vicharak-in/shrike/docs/reading_list.md

(reading_list)=
# Reading List

This is a compilation of the resources and references suggested for Shrike and FPGA in General across the web. 
 
## 1. Learning Resources 
 
1. [NandLand](https://nandland.com/learn-verilog/)
2. [Learn FPGA - B Levy](https://github.com/BrunoLevy/learn-fpga)
3. [Fpga4Fun](https://www.fpga4fun.com/)
4. [SutherLand Papers](https://sutherland-hdl.com/papers.html)
5. [FPGACPU](http://fpgacpu.ca/)
6. [ZipCpu](https://zipcpu.com/)
7. [Project F](https://projectf.io/)
8. [Verilog Pro](https://www.verilogpro.com/)
9. [AISC WORLD Verilog Tutorials ](https://www.asic-world.com/verilog/veritut.html)
10. [Lawrie FPGA Tutorials](https://lawrie.github.io/blackicemxbook/)
11. [Lut4](https://lut4.com/) 

## 2. Similar Hardware Projects 
1. [Ulx3s-Project](https://ulx3s.github.io/)
2. [TinyFPGA-Project](https://tinyfpga.com/)
3. [icebreaker-Project](https://github.com/icebreaker-fpga/icebreaker)
4. [pico-ice](https://pico-ice.tinyvision.ai/)

## 3. Communities to Join
1. Vicharak
2. ULX3S
3. TinyVision
4. 1bitsquared
