vicharak-in/shrike/Docs/index.rst

.. _shrike-home:

..
   Vicharak master file, created by
   sphinx-quickstart on Tue May  9 19:32:34 2023.
   You can adapt this file completely to your liking, but it should at least
   contain the root `toctree` directive.

.. rst-class:: lead

##############################################
 Welcome to Shrike-lite  FPGA's documentation!
##############################################

Shrike-lite is lighter version of world's first fully open source FPGA Dev board crowdsupply releasing on CrowdSupply Renesas Forge FPGA SLG47910 and RP2350.

We at vicharak have kept in mind need of a learner, maker and a hobbyist while designing this art. This dev board will be your stepping stone in the field of FPGA , reconfigurable and heterogenous computing.



.. toctree::
   :glob:
   :caption: Contents
   :titlesonly:

   Introduction <introduction>
   Hardware Overview <hardware_overview>
   Getting Started <getting_started> 
   Tools Setup <tools_setup_guide>
   Generating Bitstream <generating_your_first_bitstream>
   Verilog Style Guide <verilog_style_guide>      
   Shrike Pinouts <shrike_pinouts>
   Shrike CLI Guide <shrike_cli_guide>
   Reading List <reading_list>

.. note::

   We welcome contributions and bug reports through our `GitHub
   repository <https://github.com/vicharak-in/shrike-lite>`_.
