vicharak-in/shrike/utils/shrike-fi_web_flasher/arduino-ide/images/WabPage.png

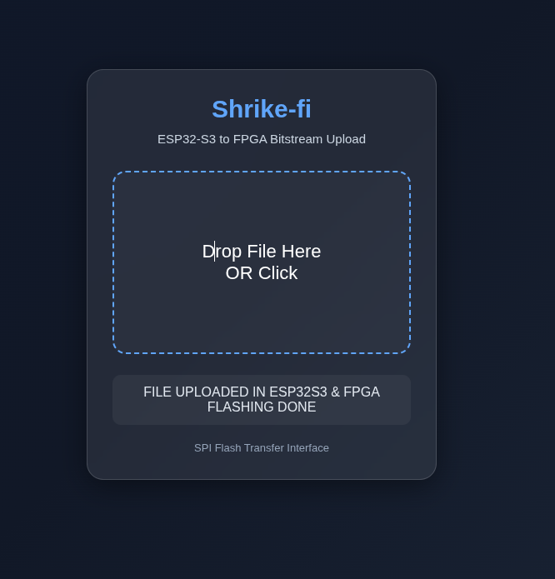
utils/shrike-fi_web_flasher/arduino-ide/images/WabPage.png
