vicharak-in/shrike/test/shrike-fi/Images/PSRAM not found.png

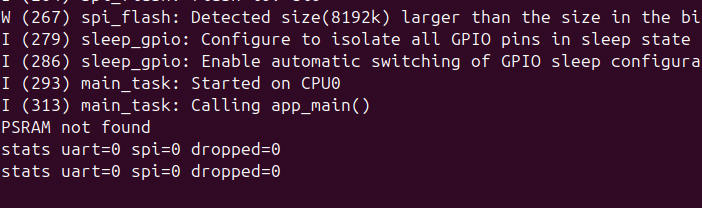
test/shrike-fi/Images/PSRAM not found.png
