vicharak-in/shrike/examples/shrike_serv/programs/nolibc.c

// nolibc.c -- the handful of freestanding routines gcc may emit calls to
// (aggregate initializers, struct copies, bss/array clears) when building for
// the SERV core with -nostdlib. Compiled alongside every C program by run.py.
// Tiny and unoptimized on purpose -- correctness over speed on a bit-serial core.

typedef unsigned long size_t;

void *memcpy(void *dst, const void *src, size_t n) {
    unsigned char *d = dst; const unsigned char *s = src;
    while (n--) *d++ = *s++;
    return dst;
}

void *memset(void *dst, int c, size_t n) {
    unsigned char *d = dst;
    while (n--) *d++ = (unsigned char)c;
    return dst;
}

void *memmove(void *dst, const void *src, size_t n) {
    unsigned char *d = dst; const unsigned char *s = src;
    if (d < s) while (n--) *d++ = *s++;
    else { d += n; s += n; while (n--) *--d = *--s; }
    return dst;
}

int memcmp(const void *a, const void *b, size_t n) {
    const unsigned char *x = a, *y = b;
    while (n--) { if (*x != *y) return *x - *y; x++; y++; }
    return 0;
}
